EcutAtom336/HeatViewer/pic/IMG_20241031_125051.jpg

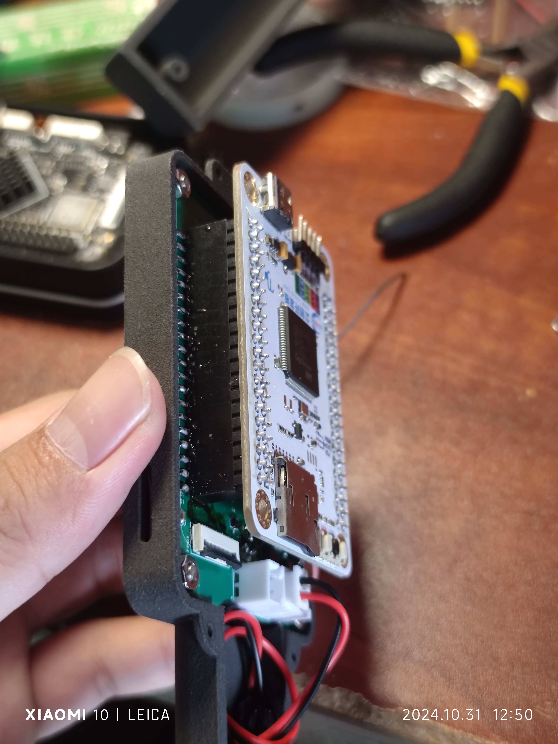
pic/IMG_20241031_125051.jpg
