EcutAtom336/HeatViewer/pic/IMG_20241031_125122.jpg

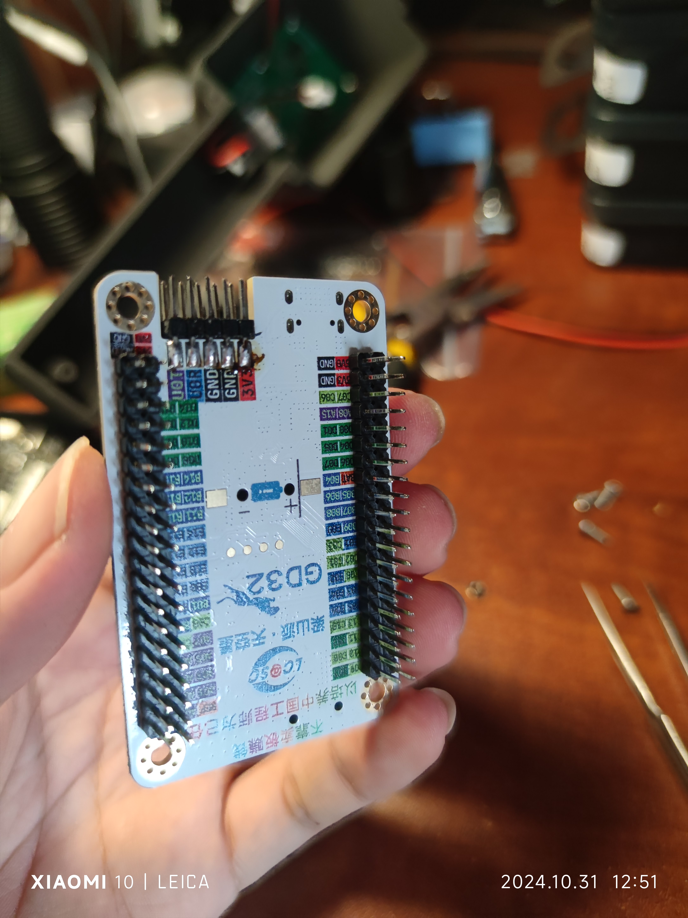
pic/IMG_20241031_125122.jpg
