EcutAtom336/HeatViewer/pic/IMG_20241031_125258.jpg

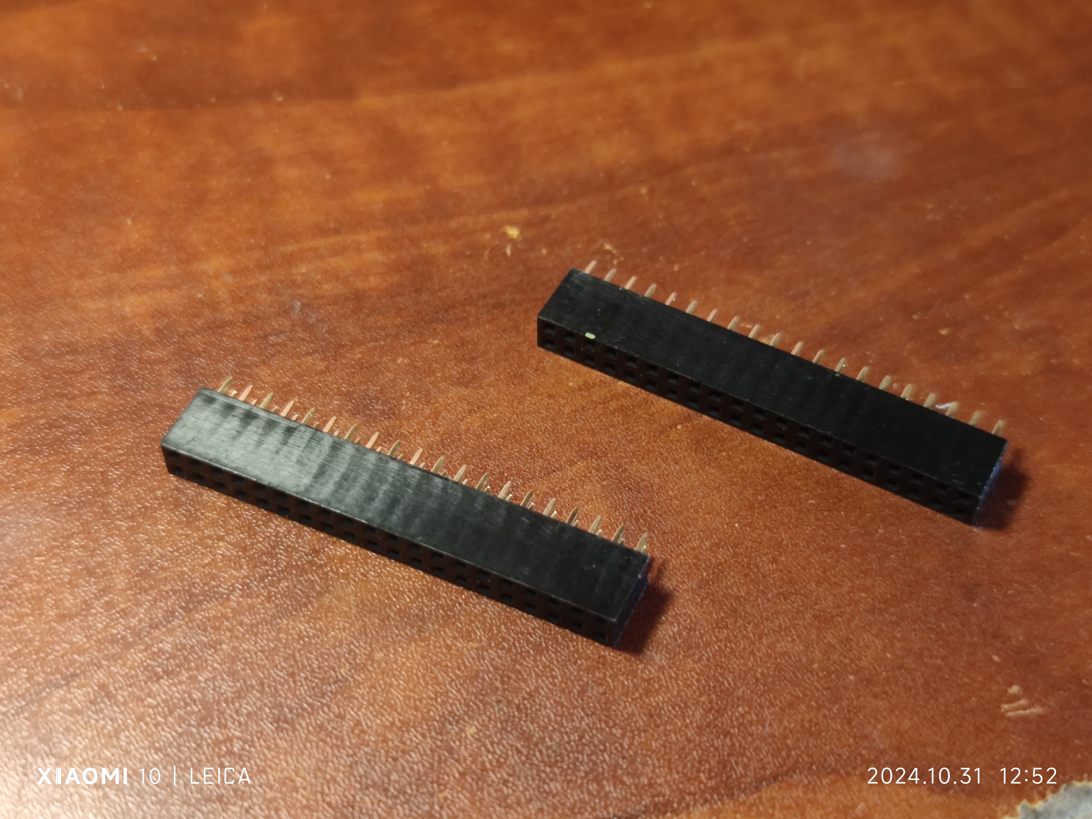
pic/IMG_20241031_125258.jpg
